grodansparadis/can4vscp-power-injector/docs/images/power_injector1.png

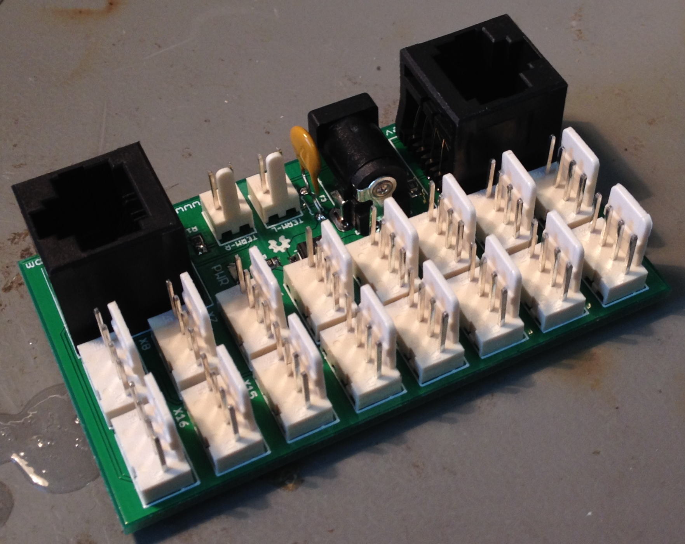
docs/images/power_injector1.png
