grodansparadis/can4vscp-power-injector/docs/images/power_injector2.png

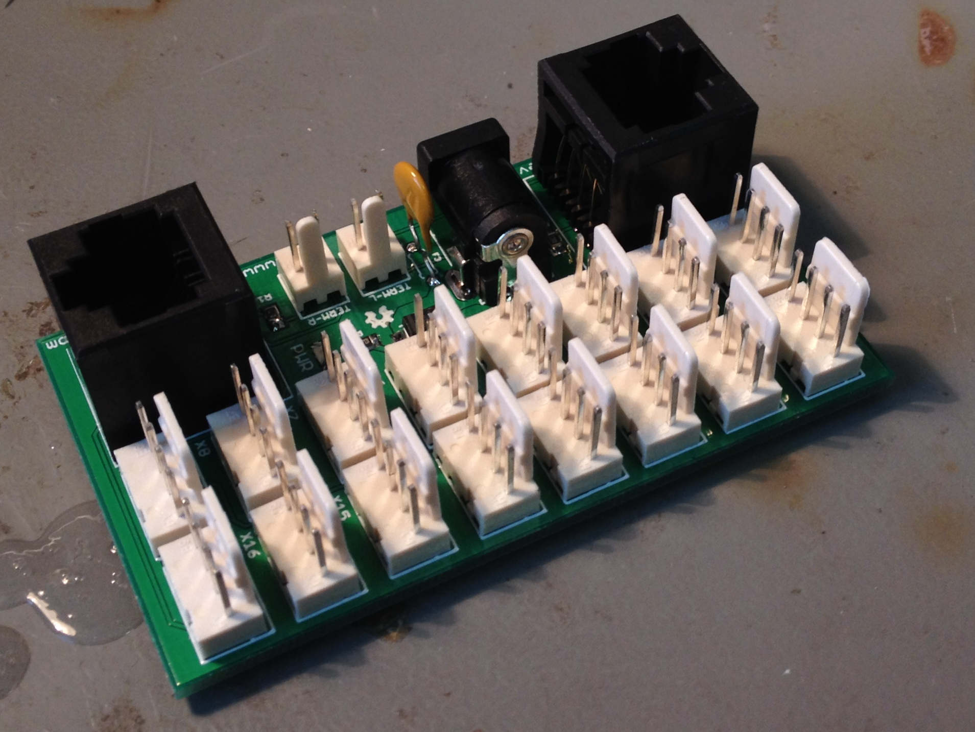
docs/images/power_injector2.png
