grodansparadis/can4vscp-power-injector/docs/images/power_injector4.png

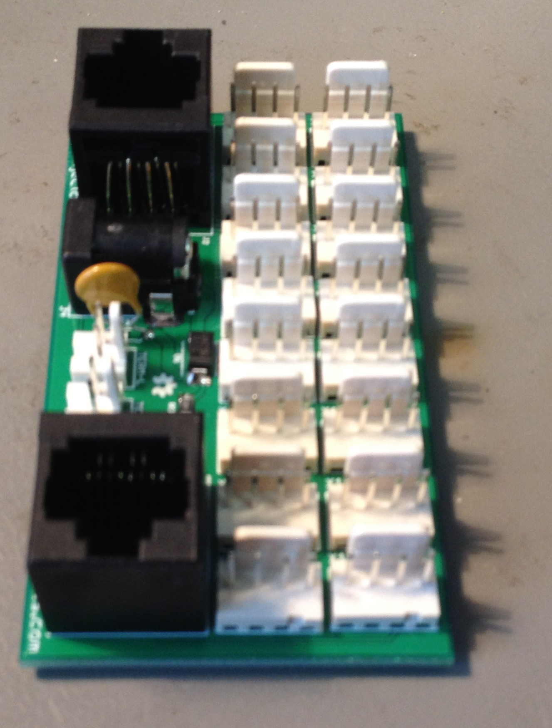
docs/images/power_injector4.png
