grodansparadis/can4vscp-power-injector/docs/images/power_injector5.png

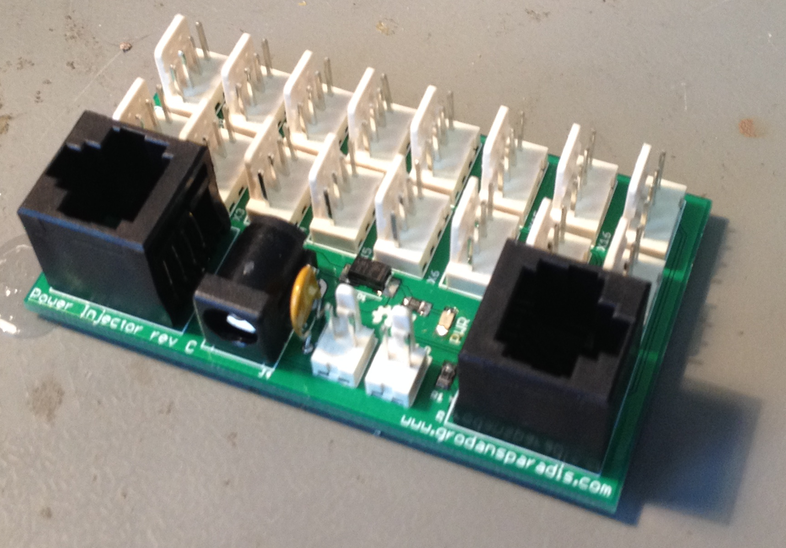
docs/images/power_injector5.png
