grodansparadis/can4vscp-power-injector/docs/images/power_injector11.png

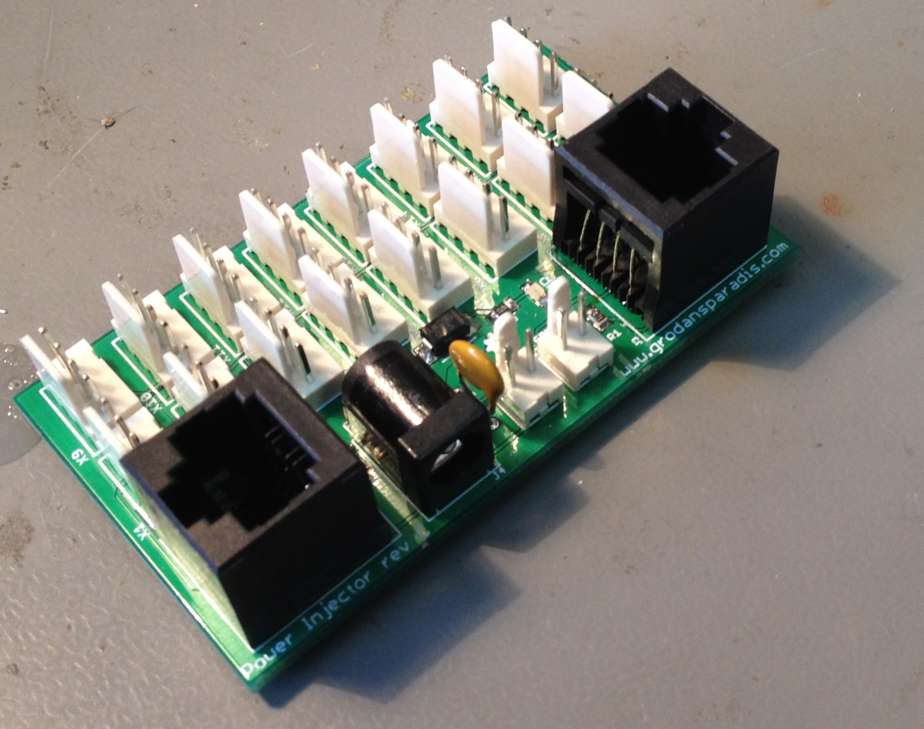
docs/images/power_injector11.png
